sonarkon/HOPE-TV/hopetv/data/slideshow/03.jpg

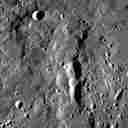
hopetv/data/slideshow/03.jpg
