sonarkon/HOPE-TV/hopetv/data/32_bagger.jpg

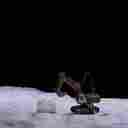
hopetv/data/32_bagger.jpg
