sonarkon/HOPE-TV/hopetv/data/03_mond_1.jpg

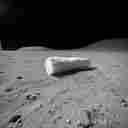
hopetv/data/03_mond_1.jpg
