sonarkon/HOPE-TV/hopetv/data/04_mond_2.jpg

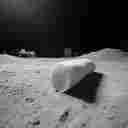
hopetv/data/04_mond_2.jpg
