sonarkon/HOPE-TV/hopetv/data/05_mond_3.jpg

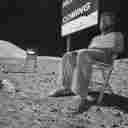
hopetv/data/05_mond_3.jpg
