sonarkon/HOPE-TV/hopetv/data/30_homebase.jpg

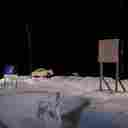
hopetv/data/30_homebase.jpg
