sonarkon/HOPE-TV/hopetv/data/31_landscape_empty.jpg

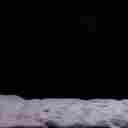
hopetv/data/31_landscape_empty.jpg
