sonarkon/HOPE-TV/hopetv/data/33_baustelle.jpg

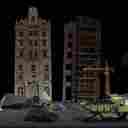
hopetv/data/33_baustelle.jpg
