sonarkon/HOPE-TV/hopetv/data/34_city.jpg

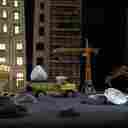
hopetv/data/34_city.jpg
