sonarkon/HOPE-TV/hopetv/data/35_dump.jpg

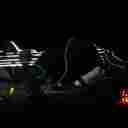
hopetv/data/35_dump.jpg
