sonarkon/HOPE-TV/hopetv/data/41_telefon.jpg

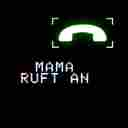
hopetv/data/41_telefon.jpg
