sonarkon/HOPE-TV/hopetv/data/slideshow/01.jpg

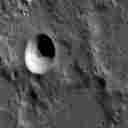
hopetv/data/slideshow/01.jpg
