sonarkon/HOPE-TV/hopetv/data/slideshow/02.jpg

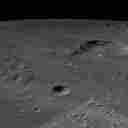
hopetv/data/slideshow/02.jpg
