sonarkon/HOPE-TV/hopetv/data/slideshow/04.jpg

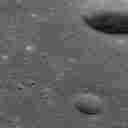
hopetv/data/slideshow/04.jpg
