sonarkon/HOPE-TV/hopetv/data/slideshow/05.jpg

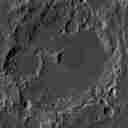
hopetv/data/slideshow/05.jpg
