sonarkon/HOPE-TV/hopetv/data/slideshow/06.jpg

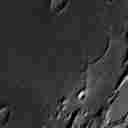
hopetv/data/slideshow/06.jpg
