sonarkon/HOPE-TV/hopetv/data/slideshow/07.jpg

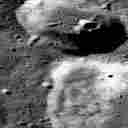
hopetv/data/slideshow/07.jpg
