sonarkon/HOPE-TV/hopetv/data/slideshow/08.jpg

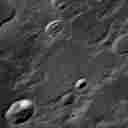
hopetv/data/slideshow/08.jpg
