sonarkon/HOPE-TV/hopetv/data/slideshow/09.jpg

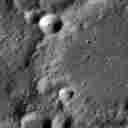
hopetv/data/slideshow/09.jpg
