sonarkon/HOPE-TV/hopetv/data/slideshow/10.jpg

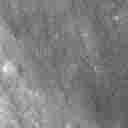
hopetv/data/slideshow/10.jpg
