sonarkon/HOPE-TV/hopetv/data/slideshow/11.jpg

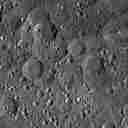
hopetv/data/slideshow/11.jpg
