sonarkon/HOPE-TV/hopetv/data/slideshow/12.jpg

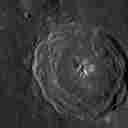
hopetv/data/slideshow/12.jpg
