sonarkon/HOPE-TV/hopetv/data/slideshow/13.jpg

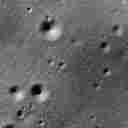
hopetv/data/slideshow/13.jpg
