sonarkon/HOPE-TV/hopetv/data/slideshow/14.jpg

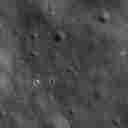
hopetv/data/slideshow/14.jpg
