sonarkon/HOPE-TV/hopetv/data/slideshow/15.jpg

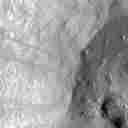
hopetv/data/slideshow/15.jpg
