sonarkon/HOPE-TV/hopetv/data/slideshow/16.jpg

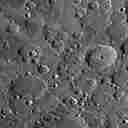
hopetv/data/slideshow/16.jpg
