sonarkon/HOPE-TV/hopetv/data/slideshow/17.jpg

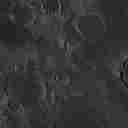
hopetv/data/slideshow/17.jpg
