sonarkon/HOPE-TV/hopetv/data/slideshow/18.jpg

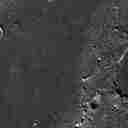
hopetv/data/slideshow/18.jpg
